FEEIT-Assistive-Technologies/Assistive-keyboard/hardware/kicad/Keyboard_Prototype.kicad_sch

## KiCad design hardware/kicad/Keyboard_Prototype.kicad_sch (2025-11-29)

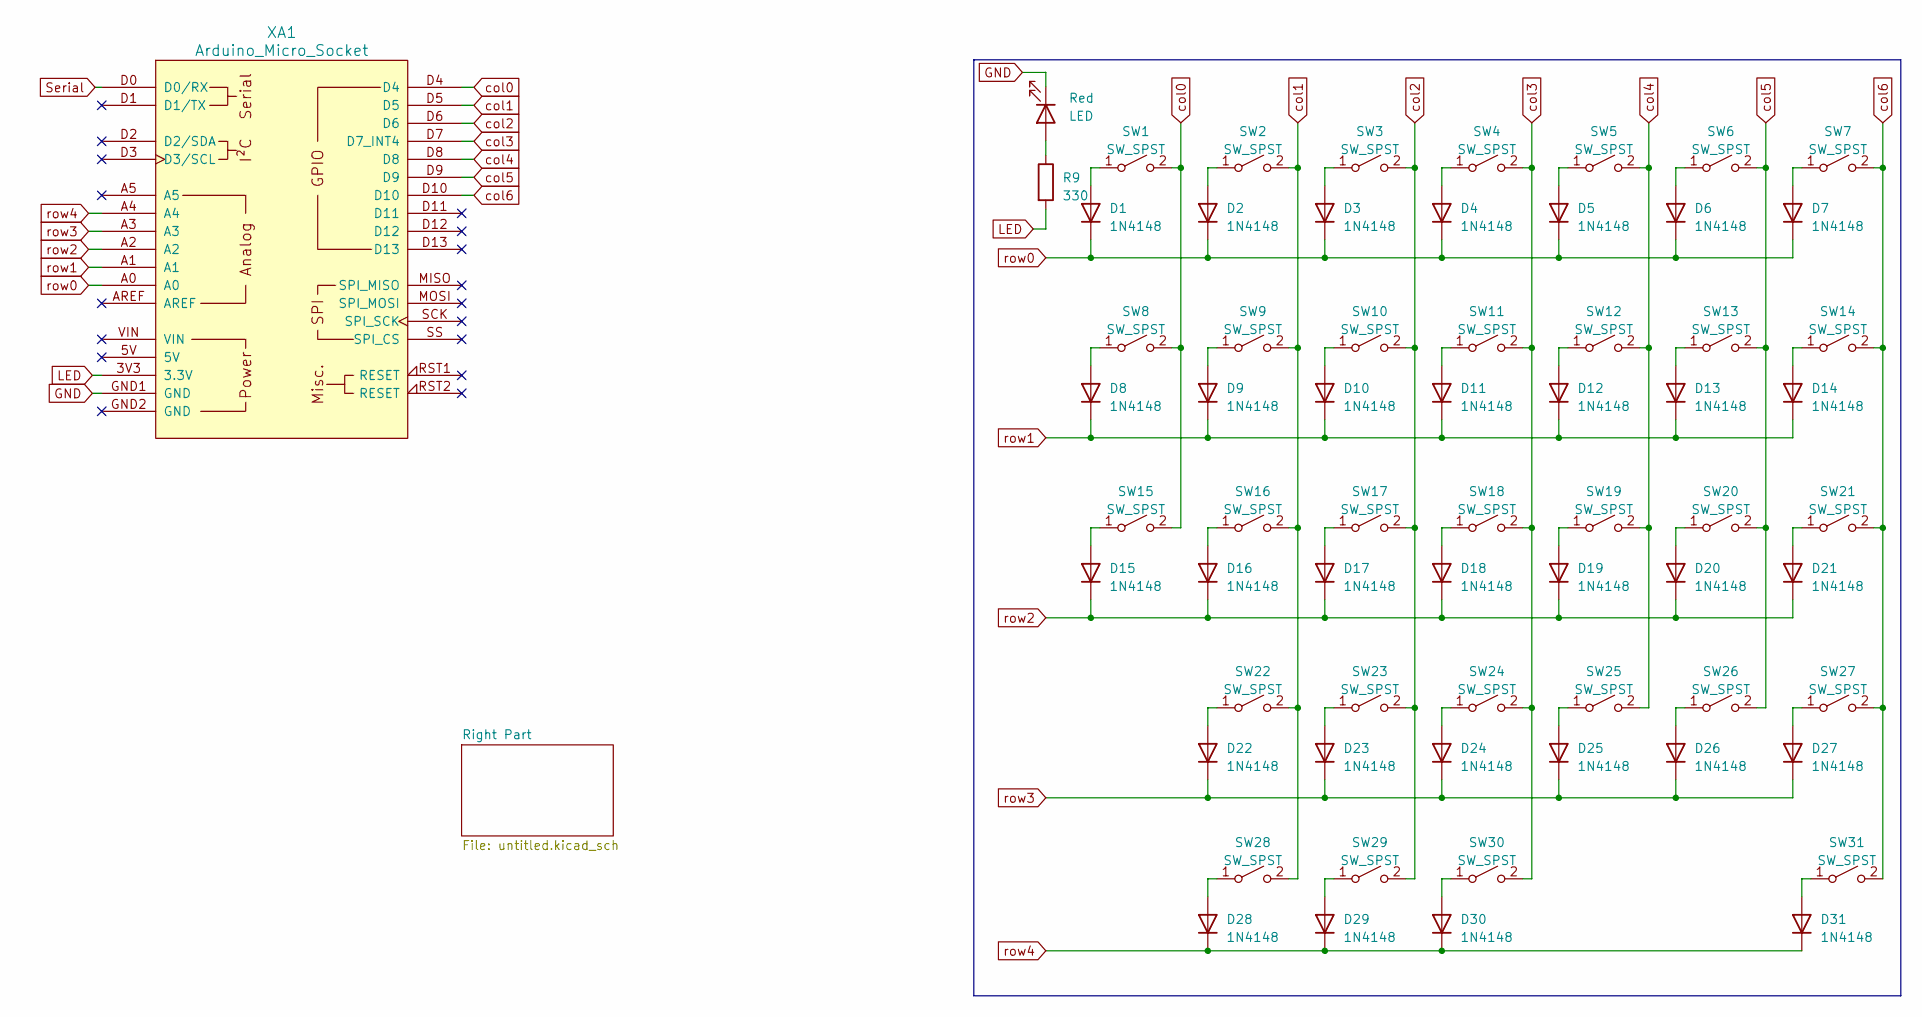
[picture p14: schematic Keyboard_Prototype.kicad_sch]

Parts:
D1, D2, D3, D4, D5, D6, D7, D8, D9, D10, D11, D12, D13, D14, D15, D16, D17, D18, D19, D20, D21, D22, D23, D24, D25, D26, D27, D28, D29, D30, D31: 1N4148; D_DO-35_SOD27_P7.62mm_Horizontal
R9: 330
Red: LED
SW1, SW2, SW3, SW4, SW5, SW6, SW7, SW8, SW9, SW10, SW11, SW12, SW13, SW14, SW15, SW16, SW17, SW18, SW19, SW20, SW21, SW22, SW23, SW24, SW25, SW26, SW27, SW28, SW29, SW30, SW31: SW_SPST
XA1: Arduino_Micro_Socket

Connections:
GND: Red.1 (K), XA1.GND1 (GND)
LED: R9.2, XA1.3V3 (3.3V)
unnamed: D1.2 (A), SW1.1 (A)
unnamed: D2.2 (A), SW2.1 (A)
unnamed: D3.2 (A), SW3.1 (A)
unnamed: D4.2 (A), SW4.1 (A)
unnamed: D5.2 (A), SW5.1 (A)
unnamed: D6.2 (A), SW6.1 (A)
unnamed: D7.2 (A), SW7.1 (A)
unnamed: D8.2 (A), SW8.1 (A)
unnamed: D9.2 (A), SW9.1 (A)
unnamed: D10.2 (A), SW10.1 (A)
unnamed: D11.2 (A), SW11.1 (A)
unnamed: D12.2 (A), SW12.1 (A)
unnamed: D13.2 (A), SW13.1 (A)
unnamed: D14.2 (A), SW14.1 (A)
unnamed: D15.2 (A), SW15.1 (A)
unnamed: D16.2 (A), SW16.1 (A)
unnamed: D17.2 (A), SW17.1 (A)
unnamed: D18.2 (A), SW18.1 (A)
unnamed: D19.2 (A), SW19.1 (A)
unnamed: D20.2 (A), SW20.1 (A)
unnamed: D21.2 (A), SW21.1 (A)
unnamed: D22.2 (A), SW22.1 (A)
unnamed: D23.2 (A), SW23.1 (A)
unnamed: D24.2 (A), SW24.1 (A)
unnamed: D25.2 (A), SW25.1 (A)
unnamed: D26.2 (A), SW26.1 (A)
unnamed: D27.2 (A), SW27.1 (A)
unnamed: D28.2 (A), SW28.1 (A)
unnamed: D29.2 (A), SW29.1 (A)
unnamed: D30.2 (A), SW30.1 (A)
unnamed: D31.2 (A), SW31.1 (A)
unnamed: R9.1, Red.2 (A)
Serial: XA1.D0 (D0/RX)
col0: SW1.2 (B), SW8.2 (B), SW15.2 (B), XA1.D4
col1: SW2.2 (B), SW9.2 (B), SW16.2 (B), SW22.2 (B), SW28.2 (B), XA1.D5
col2: SW3.2 (B), SW10.2 (B), SW17.2 (B), SW23.2 (B), SW29.2 (B), XA1.D6
col3: SW4.2 (B), SW11.2 (B), SW18.2 (B), SW24.2 (B), SW30.2 (B), XA1.D7 (D7_INT4)
col4: SW5.2 (B), SW12.2 (B), SW19.2 (B), SW25.2 (B), XA1.D8
col5: SW6.2 (B), SW13.2 (B), SW20.2 (B), SW26.2 (B), XA1.D9
col6: SW7.2 (B), SW14.2 (B), SW21.2 (B), SW27.2 (B), SW31.2 (B), XA1.D10
row0: D1.1 (K), D2.1 (K), D3.1 (K), D4.1 (K), D5.1 (K), D6.1 (K), D7.1 (K), XA1.A0
row1: D8.1 (K), D9.1 (K), D10.1 (K), D11.1 (K), D12.1 (K), D13.1 (K), D14.1 (K), XA1.A1
row2: D15.1 (K), D16.1 (K), D17.1 (K), D18.1 (K), D19.1 (K), D20.1 (K), D21.1 (K), XA1.A2
row3: D22.1 (K), D23.1 (K), D24.1 (K), D25.1 (K), D26.1 (K), D27.1 (K), XA1.A3
row4: D28.1 (K), D29.1 (K), D30.1 (K), D31.1 (K), XA1.A4
