FEEIT-Assistive-Technologies/Assistive-keyboard/hardware/kicad/untitled.kicad_sch

## KiCad design hardware/kicad/untitled.kicad_sch (2025-04-20)

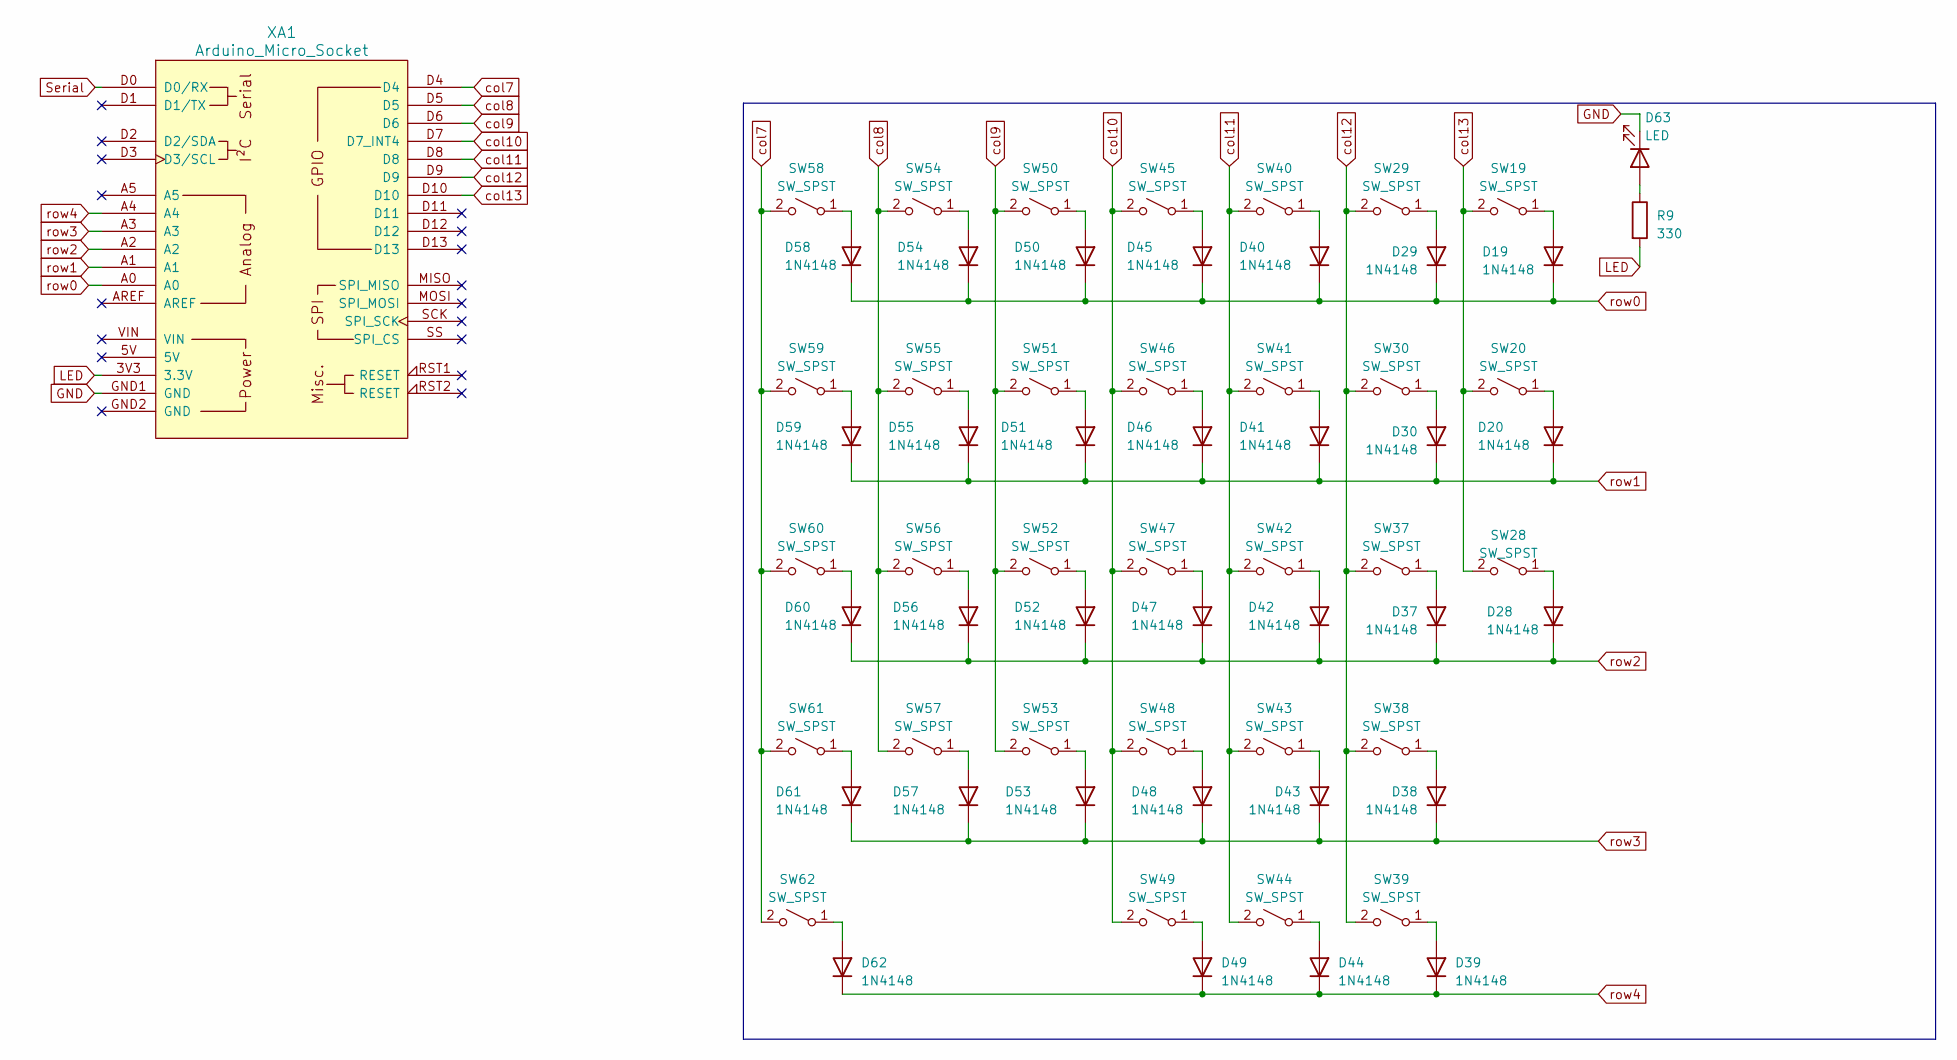
[picture p15: schematic untitled.kicad_sch]

Parts:
D19, D20, D28, D29, D30, D37, D38, D39, D40, D41, D42, D43, D44, D45, D46, D47, D48, D49, D50, D51, D52, D53, D54, D55, D56, D57, D58, D59, D60, D61, D62: 1N4148; D_DO-35_SOD27_P7.62mm_Horizontal
D63: LED
R9: 330
SW19, SW20, SW28, SW29, SW30, SW37, SW38, SW39, SW40, SW41, SW42, SW43, SW44, SW45, SW46, SW47, SW48, SW49, SW50, SW51, SW52, SW53, SW54, SW55, SW56, SW57, SW58, SW59, SW60, SW61, SW62: SW_SPST
XA1: Arduino_Micro_Socket

Connections:
GND: D63.1 (K), XA1.GND1 (GND)
LED: R9.2, XA1.3V3 (3.3V)
unnamed: D19.2 (A), SW19.1 (A)
unnamed: D20.2 (A), SW20.1 (A)
unnamed: D28.2 (A), SW28.1 (A)
unnamed: D29.2 (A), SW29.1 (A)
unnamed: D30.2 (A), SW30.1 (A)
unnamed: D37.2 (A), SW37.1 (A)
unnamed: D38.2 (A), SW38.1 (A)
unnamed: D39.2 (A), SW39.1 (A)
unnamed: D40.2 (A), SW40.1 (A)
unnamed: D41.2 (A), SW41.1 (A)
unnamed: D42.2 (A), SW42.1 (A)
unnamed: D43.2 (A), SW43.1 (A)
unnamed: D44.2 (A), SW44.1 (A)
unnamed: D45.2 (A), SW45.1 (A)
unnamed: D46.2 (A), SW46.1 (A)
unnamed: D47.2 (A), SW47.1 (A)
unnamed: D48.2 (A), SW48.1 (A)
unnamed: D49.2 (A), SW49.1 (A)
unnamed: D50.2 (A), SW50.1 (A)
unnamed: D51.2 (A), SW51.1 (A)
unnamed: D52.2 (A), SW52.1 (A)
unnamed: D53.2 (A), SW53.1 (A)
unnamed: D54.2 (A), SW54.1 (A)
unnamed: D55.2 (A), SW55.1 (A)
unnamed: D56.2 (A), SW56.1 (A)
unnamed: D57.2 (A), SW57.1 (A)
unnamed: D58.2 (A), SW58.1 (A)
unnamed: D59.2 (A), SW59.1 (A)
unnamed: D60.2 (A), SW60.1 (A)
unnamed: D61.2 (A), SW61.1 (A)
unnamed: D62.2 (A), SW62.1 (A)
unnamed: D63.2 (A), R9.1
Serial: XA1.D0 (D0/RX)
col7: SW58.2 (B), SW59.2 (B), SW60.2 (B), SW61.2 (B), SW62.2 (B), XA1.D4
col8: SW54.2 (B), SW55.2 (B), SW56.2 (B), SW57.2 (B), XA1.D5
col9: SW50.2 (B), SW51.2 (B), SW52.2 (B), SW53.2 (B), XA1.D6
col10: SW45.2 (B), SW46.2 (B), SW47.2 (B), SW48.2 (B), SW49.2 (B), XA1.D7 (D7_INT4)
col11: SW40.2 (B), SW41.2 (B), SW42.2 (B), SW43.2 (B), SW44.2 (B), XA1.D8
col12: SW29.2 (B), SW30.2 (B), SW37.2 (B), SW38.2 (B), SW39.2 (B), XA1.D9
col13: SW19.2 (B), SW20.2 (B), SW28.2 (B), XA1.D10
row0: D19.1 (K), D29.1 (K), D40.1 (K), D45.1 (K), D50.1 (K), D54.1 (K), D58.1 (K), XA1.A0
row1: D20.1 (K), D30.1 (K), D41.1 (K), D46.1 (K), D51.1 (K), D55.1 (K), D59.1 (K), XA1.A1
row2: D28.1 (K), D37.1 (K), D42.1 (K), D47.1 (K), D52.1 (K), D56.1 (K), D60.1 (K), XA1.A2
row3: D38.1 (K), D43.1 (K), D48.1 (K), D53.1 (K), D57.1 (K), D61.1 (K), XA1.A3
row4: D39.1 (K), D44.1 (K), D49.1 (K), D62.1 (K), XA1.A4
